dczia/mk9-badge/hardware/images/Board_Art.png

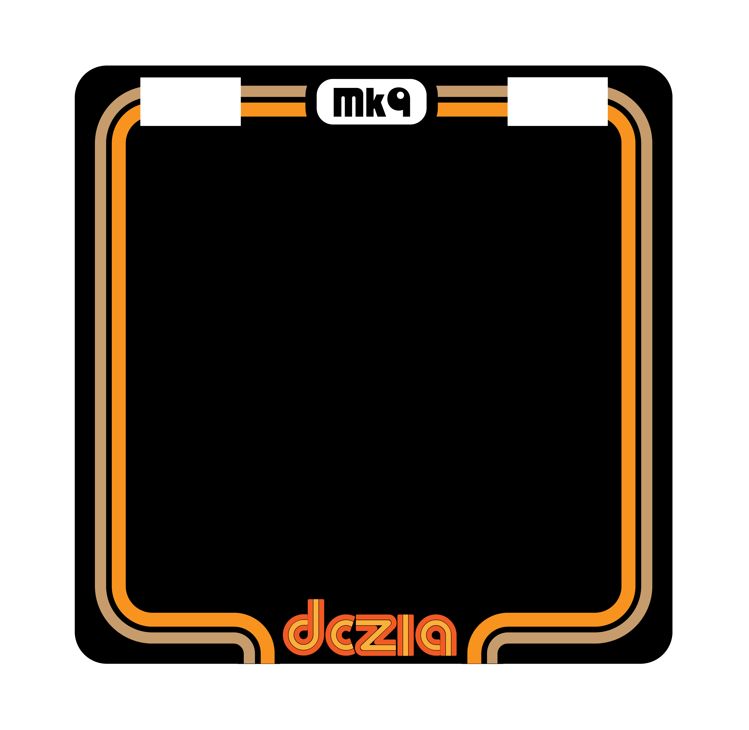
hardware/images/Board_Art.png
